securehardware-bi0s/Falcon-Badge/src/initial/data/chall.png

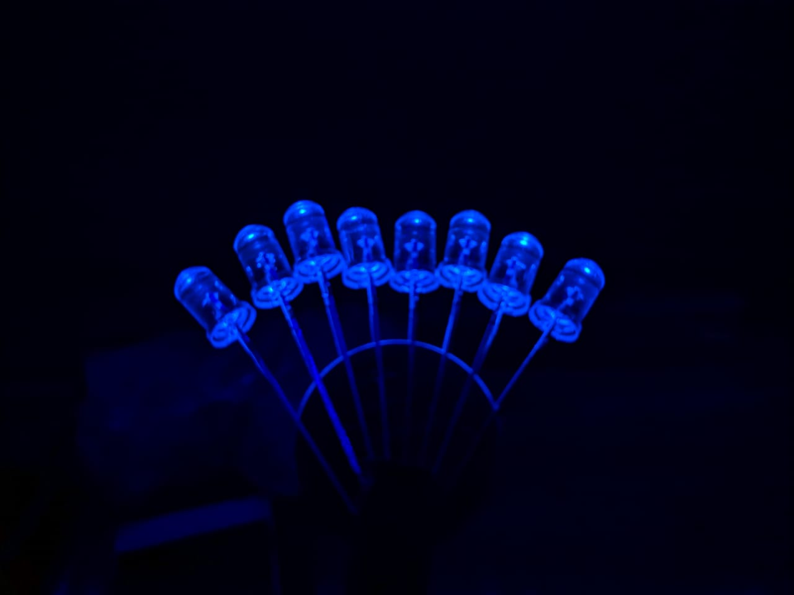
src/initial/data/chall.png
