securehardware-bi0s/Falcon-Badge/src/Final/images.h

#define Logo_width 128 
#define Logo_height 32
const uint8_t inctf[] PROGMEM = {
  0x00, 0x00, 0x00, 0x00, 0x00, 0x00, 0x00, 0x00, 0x00, 0x00, 0x00, 0x00, 
  0x00, 0x00, 0x00, 0x00, 0x00, 0x00, 0x00, 0x00, 0x00, 0x00, 0x00, 0x00, 
  0x00, 0x00, 0x00, 0x00, 0x00, 0x00, 0x00, 0x00, 0x00, 0x00, 0x00, 0x00, 
  0x00, 0x18, 0x10, 0x0C, 0x1F, 0xF2, 0x0F, 0x01, 0x00, 0x00, 0x00, 0x00, 
  0x00, 0x00, 0x00, 0x00, 0x00, 0x18, 0x38, 0x0C, 0x33, 0x83, 0x81, 0x03, 
  0x00, 0x00, 0x00, 0x00, 0x00, 0x00, 0x00, 0x00, 0x00, 0x34, 0x38, 0x1E, 
  0x33, 0x83, 0xC1, 0x03, 0x00, 0x00, 0x00, 0x00, 0x00, 0x00, 0x00, 0x00, 
  0x00, 0x76, 0x6C, 0x1A, 0x1F, 0x83, 0x41, 0x06, 0x00, 0x00, 0x00, 0x00, 
  0x00, 0x00, 0x00, 0x00, 0x00, 0x62, 0xC4, 0x31, 0x1B, 0x83, 0x61, 0x0E, 
  0x00, 0x00, 0x00, 0x00, 0x00, 0xF0, 0xFF, 0xFF, 0x3F, 0xC3, 0xC6, 0x31, 
  0x33, 0x83, 0x21, 0x8C, 0xFF, 0xFF, 0x3F, 0x00, 0x00, 0x00, 0x00, 0x00, 
  0x00, 0x81, 0x83, 0x60, 0x61, 0x82, 0x11, 0x18, 0x00, 0x00, 0x00, 0x00, 
  0x00, 0x00, 0x00, 0x00, 0x00, 0x00, 0x00, 0x00, 0x00, 0x00, 0x00, 0x00, 
  0x00, 0x00, 0x00, 0x00, 0x00, 0x00, 0x00, 0x00, 0x00, 0x00, 0xF8, 0xFF, 
  0xFF, 0xFF, 0xFF, 0x7F, 0xFC, 0xFF, 0x3F, 0x00, 0x00, 0x70, 0x00, 0x00, 
  0x00, 0x00, 0xFF, 0xFF, 0xFF, 0xFF, 0xFF, 0xBF, 0xFF, 0xFF, 0x3F, 0x00, 
  0x00, 0xF0, 0x03, 0x00, 0x00, 0x80, 0xFF, 0xFF, 0xFF, 0xFF, 0xFF, 0xBF, 
  0xFF, 0xFF, 0x3F, 0x00, 0x00, 0xF0, 0x1F, 0x00, 0x00, 0x80, 0xFF, 0xFF, 
  0xFF, 0xFF, 0xFF, 0xDF, 0xFF, 0xFF, 0x3F, 0x00, 0x00, 0xF0, 0x1F, 0x00, 
  0x00, 0x80, 0xFF, 0xFF, 0xFF, 0xFF, 0xFF, 0xFF, 0xFF, 0xFF, 0x3F, 0x00, 
  0x00, 0xF0, 0x1F, 0x00, 0x00, 0x80, 0xFF, 0x01, 0x00, 0xE0, 0x3F, 0xC0, 
  0xFF, 0x00, 0x00, 0x00, 0x00, 0xF0, 0x1F, 0x00, 0x00, 0x80, 0xFF, 0x00, 
  0x00, 0xE0, 0x3F, 0xC0, 0x7F, 0x00, 0x00, 0x00, 0x00, 0xF0, 0x1F, 0x00, 
  0x00, 0x80, 0xFF, 0x00, 0x00, 0xE0, 0x3F, 0xC0, 0x7F, 0x00, 0x00, 0x00, 
  0x00, 0xF0, 0x1F, 0x00, 0x00, 0x80, 0xFF, 0x00, 0x00, 0xE0, 0x3F, 0xC0, 
  0x7F, 0x00, 0x00, 0x00, 0x00, 0xF0, 0x1F, 0xFF, 0xFF, 0x8F, 0xFF, 0x00, 
  0x00, 0xE0, 0x3F, 0xC0, 0xFF, 0xFF, 0x03, 0x00, 0x00, 0xF0, 0x9F, 0xFF, 
  0xFF, 0x9F, 0xFF, 0x00, 0x00, 0xE0, 0x3F, 0xC0, 0xFF, 0xFF, 0x03, 0x00, 
  0x00, 0xF0, 0x9F, 0xFF, 0xFF, 0xBF, 0xFF, 0x00, 0x00, 0xE0, 0x3F, 0xC0, 
  0xFF, 0xFF, 0x03, 0x00, 0x00, 0xF0, 0x9F, 0xFF, 0xFF, 0xBF, 0xFF, 0x00, 
  0x00, 0xE0, 0x3F, 0xC0, 0xFF, 0xFF, 0x03, 0x00, 0x00, 0xF0, 0x9F, 0xFF, 
  0xE0, 0xBF, 0xFF, 0x00, 0x00, 0xE0, 0x3F, 0xC0, 0xFF, 0xFF, 0x03, 0x00, 
  0x00, 0xF0, 0x9F, 0xFF, 0xE0, 0xBF, 0xFF, 0x00, 0x00, 0xE0, 0x3F, 0xC0, 
  0x7F, 0x00, 0x00, 0x00, 0x00, 0xF0, 0x9F, 0xFF, 0xE0, 0xBF, 0xFF, 0x00, 
  0x00, 0xE0, 0x3F, 0xC0, 0x7F, 0x00, 0x00, 0x00, 0x00, 0xF0, 0x9F, 0xFF, 
  0xE0, 0xBF, 0xFF, 0xFF, 0x7F, 0xE0, 0x3F, 0x00, 0x7F, 0x00, 0x00, 0x00, 
  0x00, 0xF0, 0x9F, 0xFF, 0xE0, 0xBF, 0xFF, 0xFF, 0xFF, 0xE0, 0x3F, 0x00, 
  0x7C, 0x00, 0x00, 0x00, 0x00, 0xF0, 0x9F, 0xFF, 0xE0, 0xBF, 0xFF, 0xFF, 
  0xFF, 0xE1, 0x3F, 0x00, 0x78, 0x00, 0x00, 0x00, 0x00, 0xF0, 0x9F, 0xFF, 
  0xE0, 0x3F, 0xFF, 0xFF, 0xFF, 0xE3, 0x3F, 0x00, 0x60, 0x00, 0x00, 0x00, 
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
